SamFat787/SmartDenProject/IMG_2177.jpg

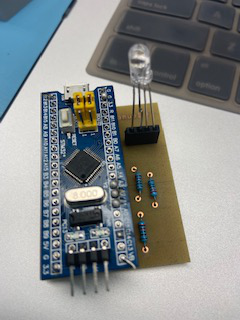
IMG_2177.jpg
